kgat96/ubermini/hardware/cc2400dbk/CC2430-CC2591EM_2_0_Schematic.pdf

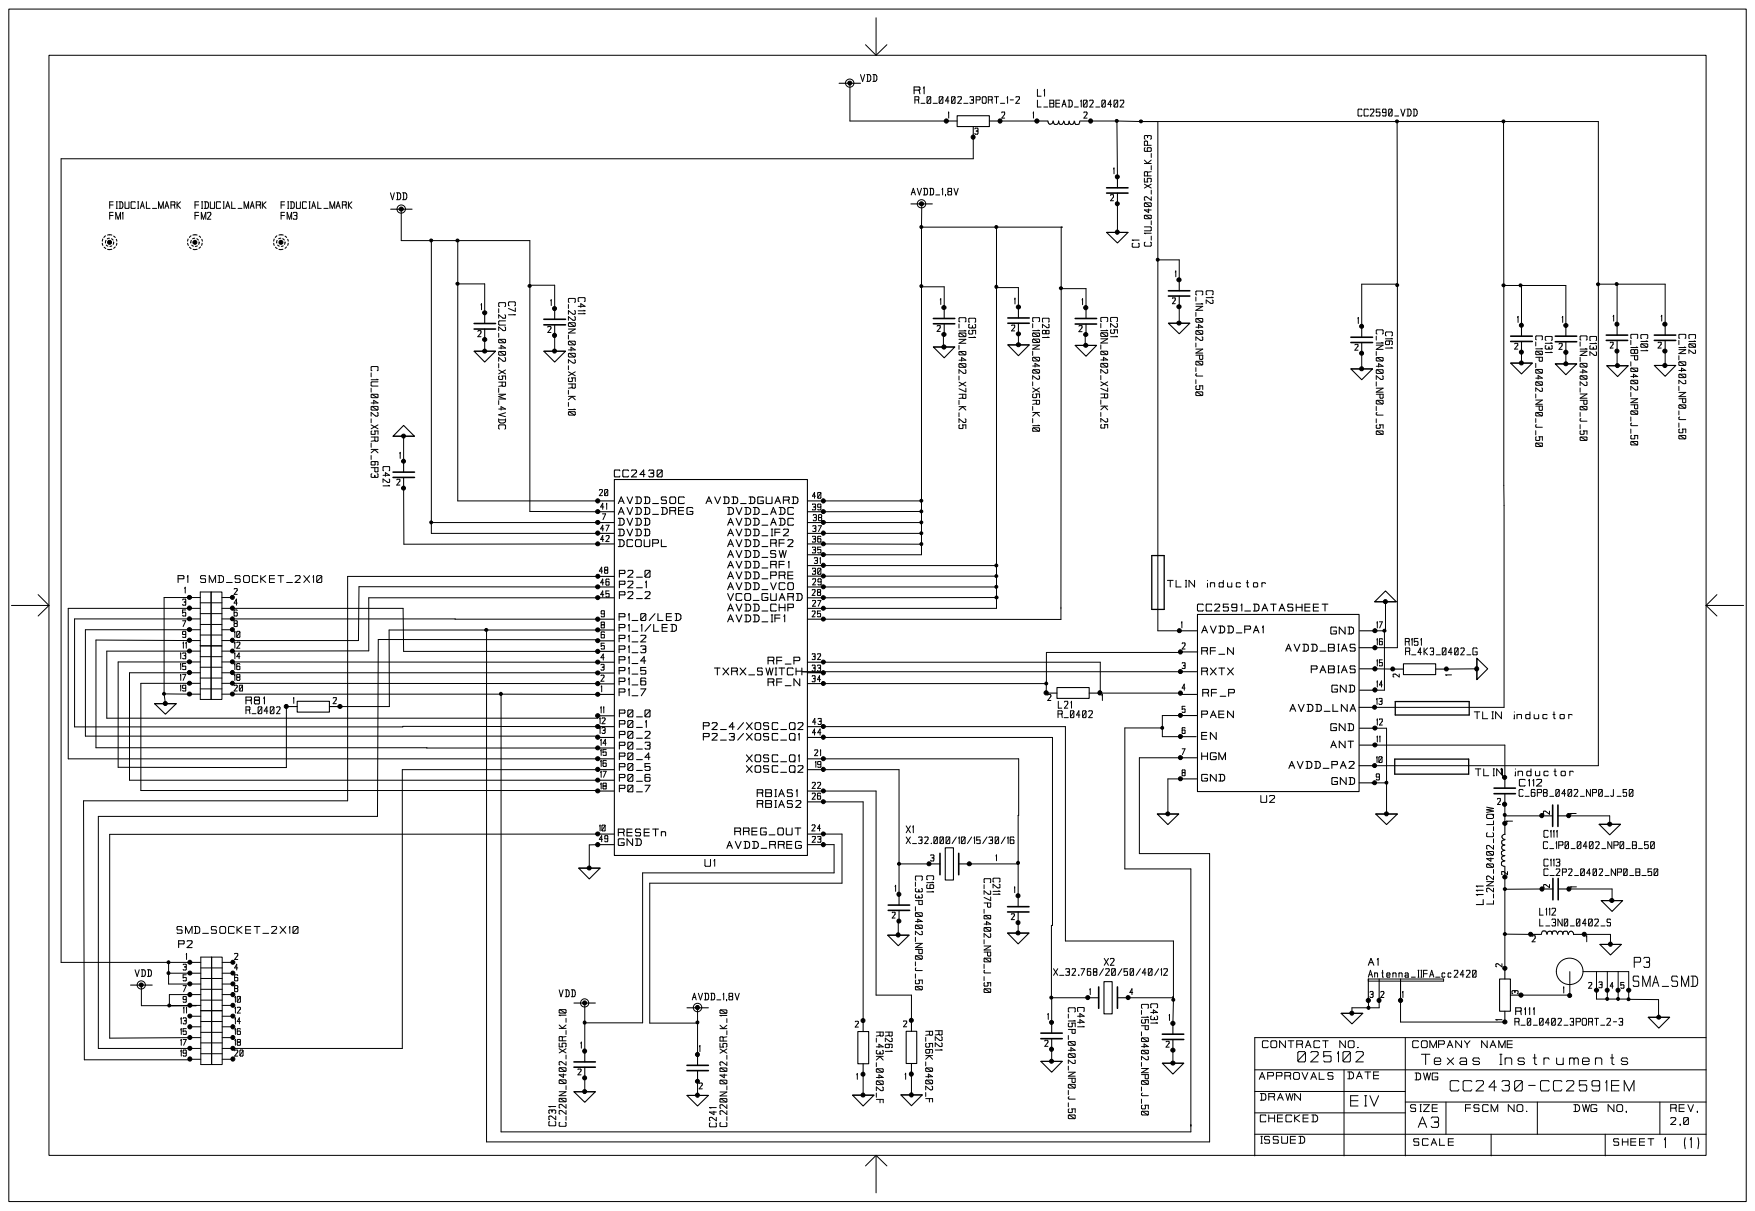
[picture p29: page 1]
