kgat96/ubermini/hardware/v1/ubertoothpV1.pdf

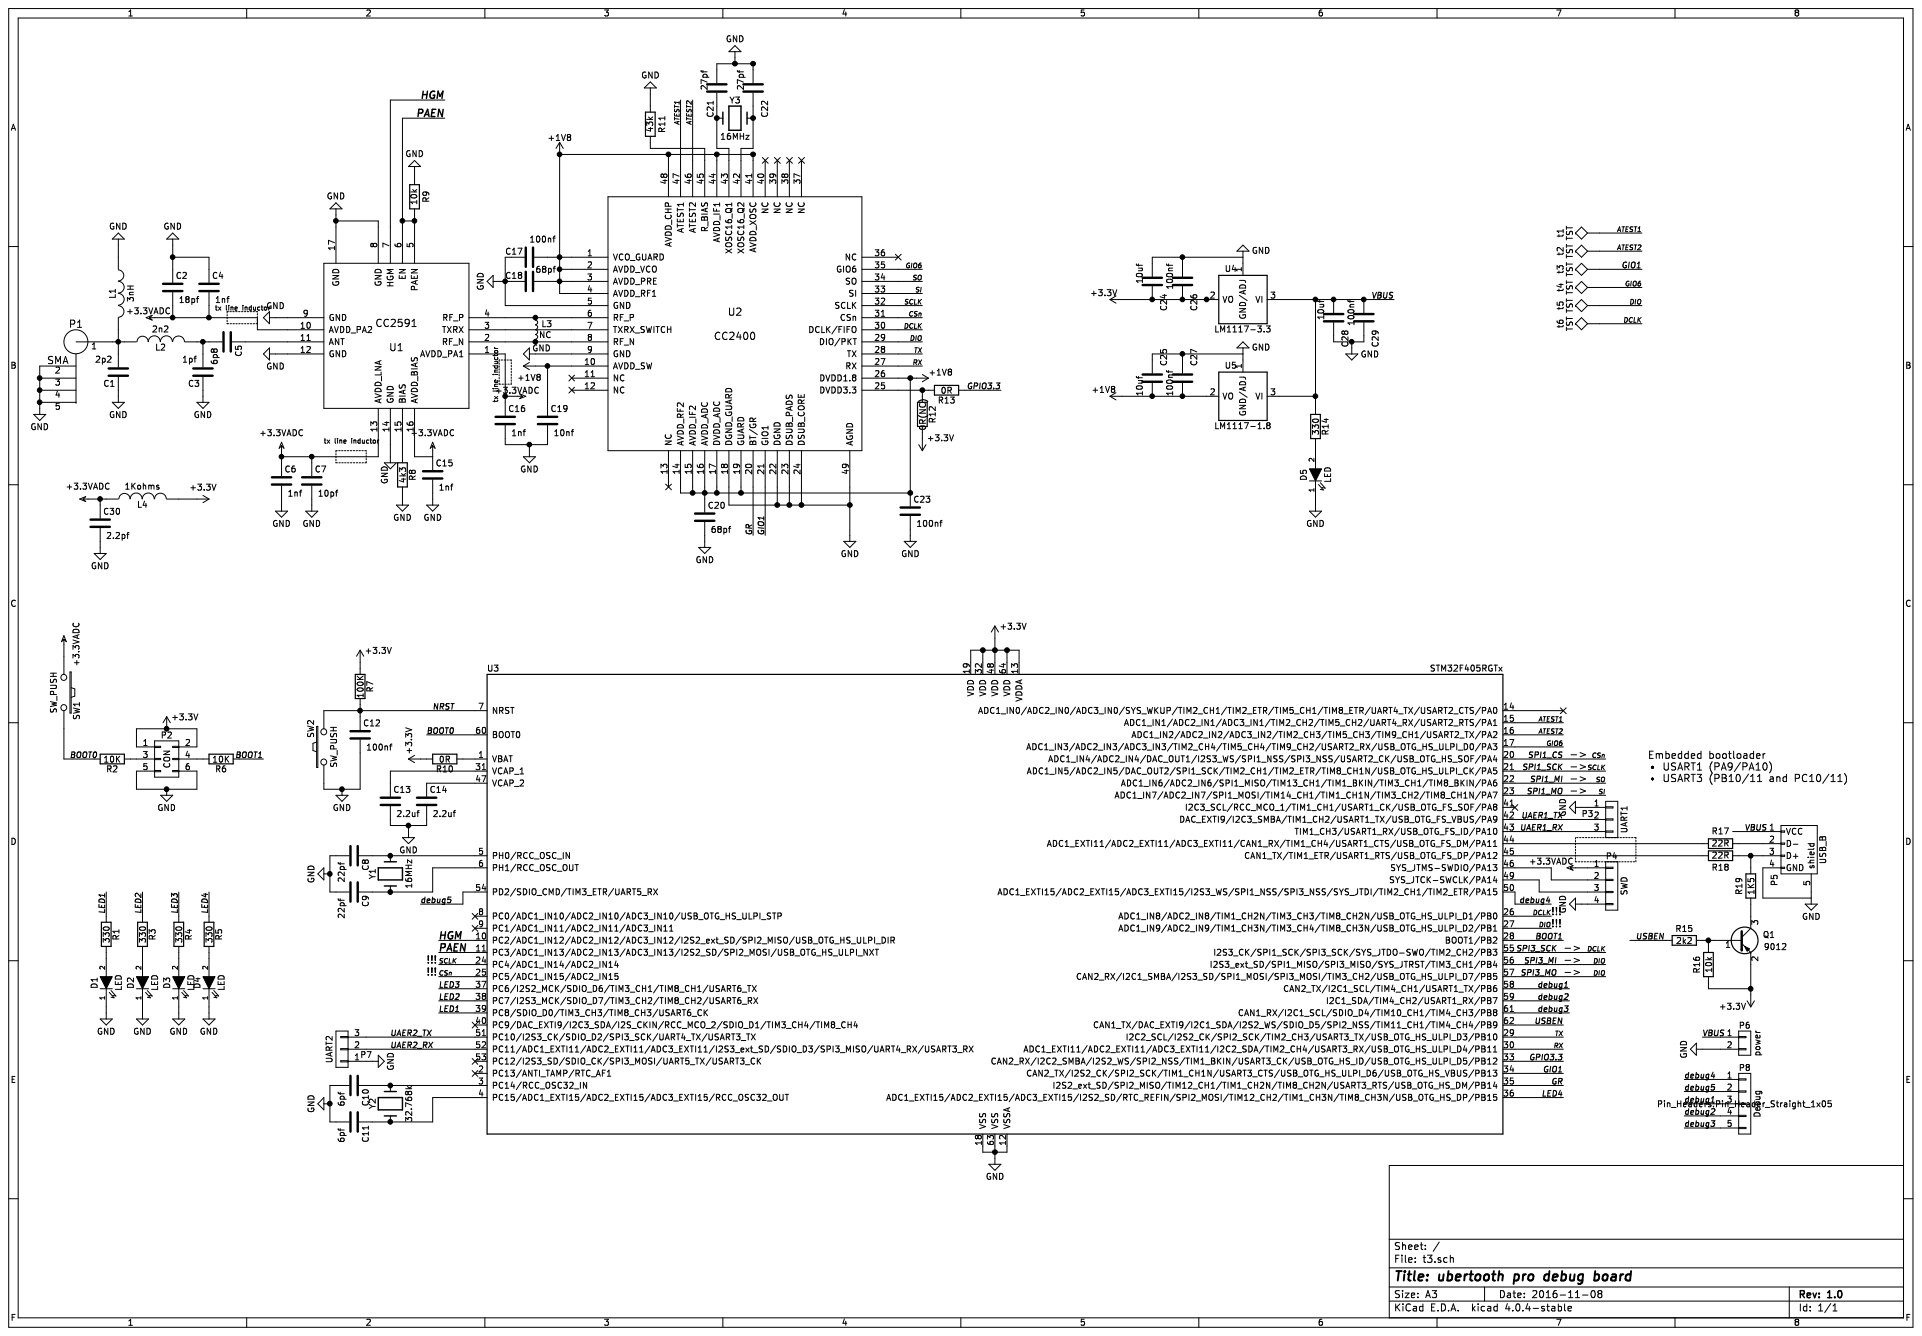
[picture p30: page 1]
