kgat96/ubermini/uber/hardware/artichoke/artichoke.sch

## KiCad design uber/hardware/artichoke/artichoke.sch (2016-11-08)

Schematic: artichoke.sch

Parts:
C1, C4, C22: 100nF
C2, C3, C6, C9, C15, C18, C20, C21: 27pF
C5, C17, C19: 220nF
C12, C16: 1pF; 0402
C13, C14: 10nF
C23, C24: 18pF
C25: 1µF; 0603
C26, C27, C28, C30, C31, C33, C34: 100nF; 0603
C29: 2.2µF; 0603
C32, C35: 18pF; 0603
D2: TXLED; 0603D
D3: RXLED; 0603D
D4: USRLED; 0603D
D5: RSTLED; 0603D
D6: USBLED; 0603D
J1: USB-DEVICE; USB-A-USAM-04
L1, L3: 2n7
L2: 9n5
P1: SMA-CONN; SMA-EDGE
P2: PROGRAM; 100MIL-HEADER-1X6-EDGE
P3: JTAG; 50MIL-HEADER-2X5-TH
P4: EXPAND; PIN_ARRAY_3X2
P6: 3V3D; testpad-50mil
P7: VBUS; testpad-50mil
P8: ATB
P11: TRCLK; testpad-50mil
P12: DT; testpad-50mil
P13: DR; testpad-50mil
Q1: BC856; SOT416
R1, R9, R10, R14: 10k; 0603
R2: 27k
R5, R6: 470; 0603
R7, R8, R15: 330; 0603
R11: 2k2; 0603
R12, R13: 33; 0603
R16: 1k5; 0603
U1: SI9183-A
U2: ADF7242
U4: LPC175X; LQFP80
U6: IP4220CZ6; SOT457
X1: NX3225SA; ABMM2
X2: ABM8G

Notes on the sheet:
test points
expansion connector
JTAG connector
programming connector
