kgat96/ubermini/uber/hardware/tc13badge/tc13badge.sch

## KiCad design uber/hardware/tc13badge/tc13badge.sch (2016-11-08)

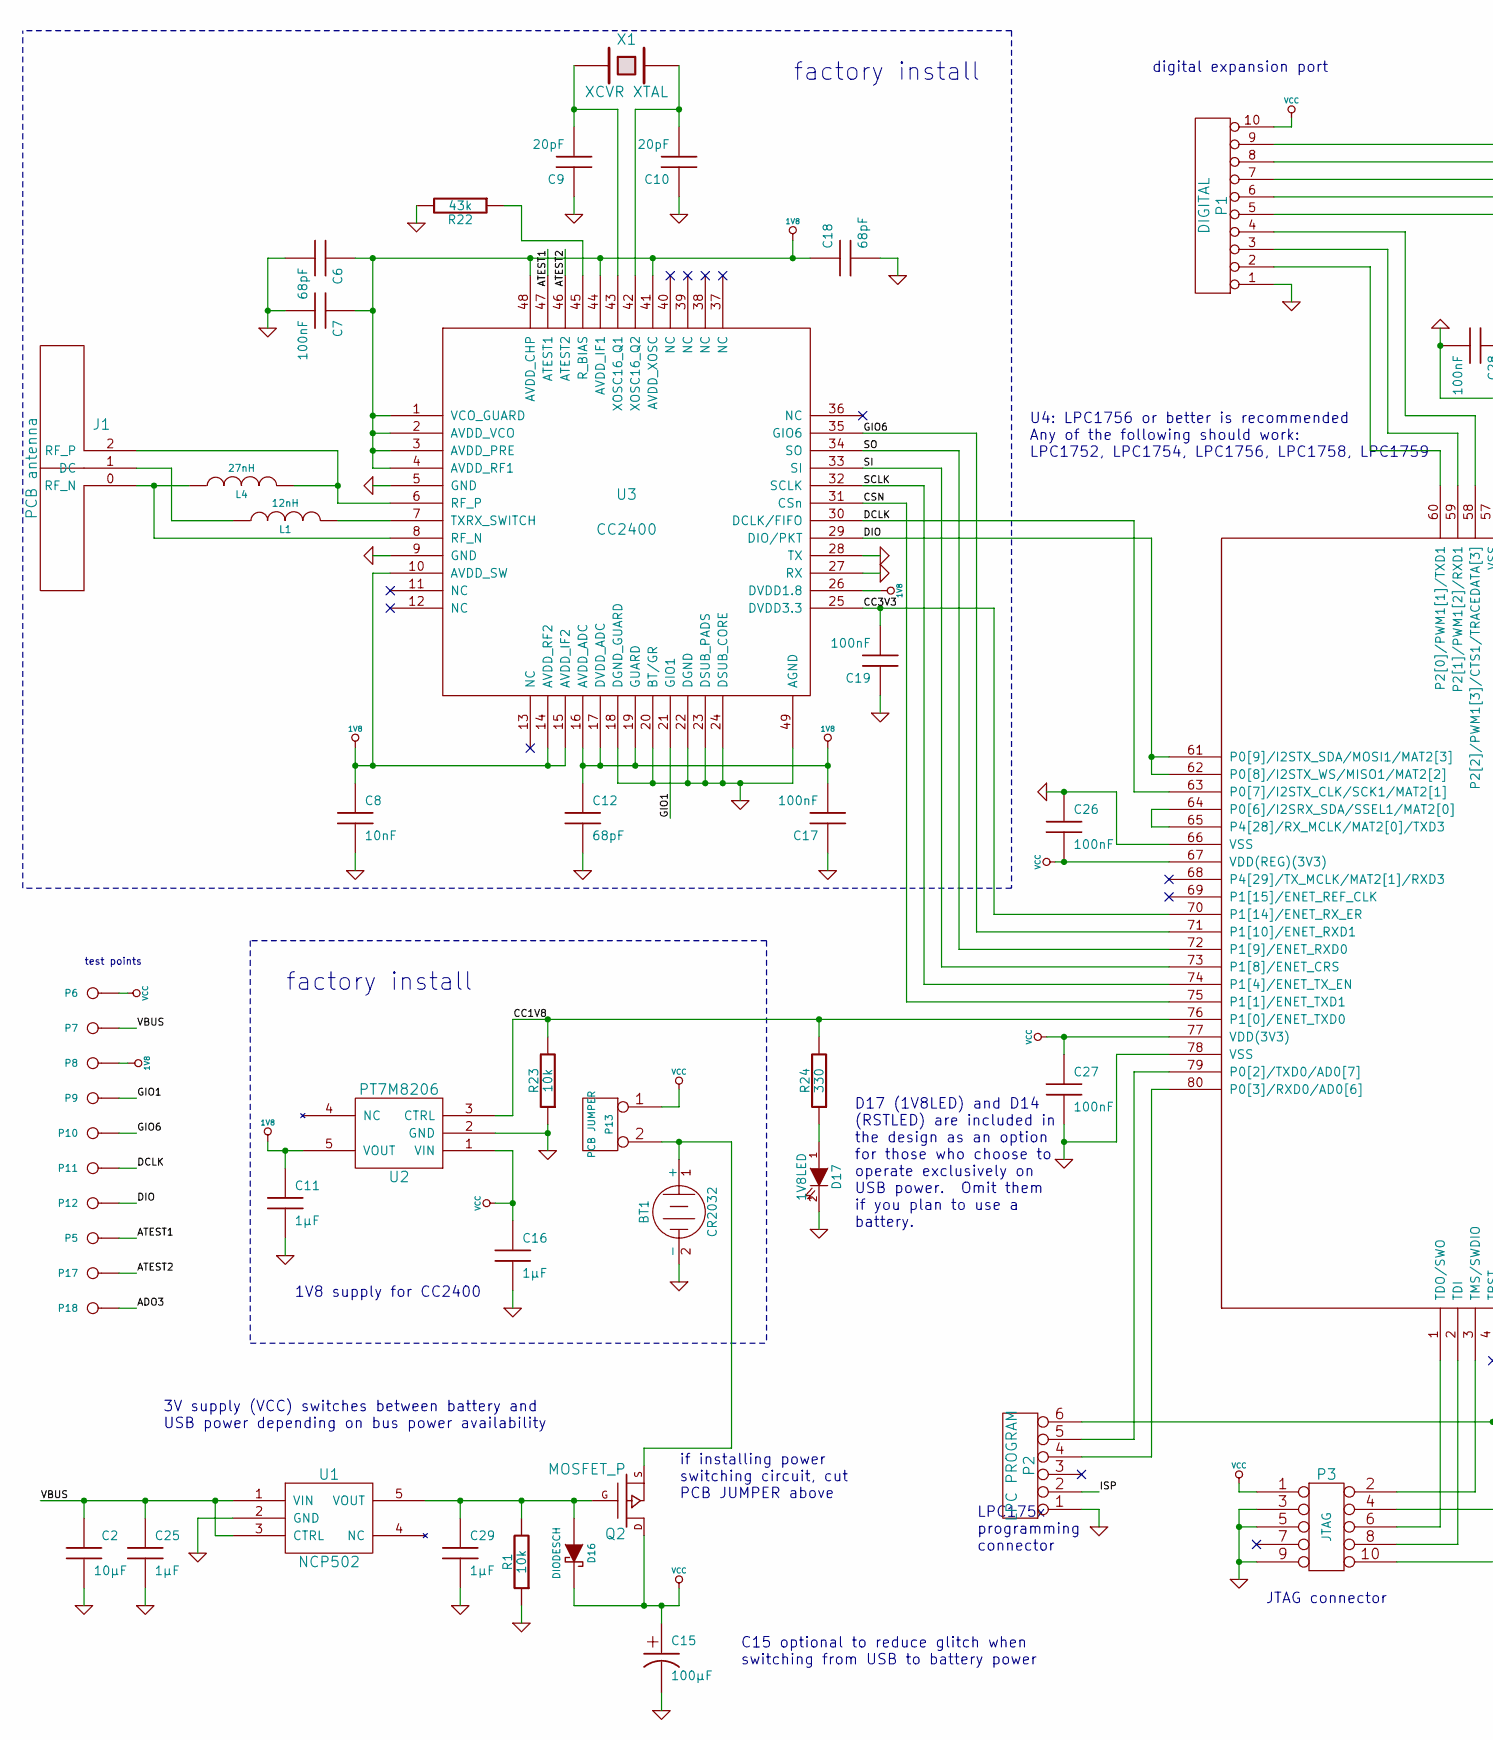
[picture p44: schematic tc13badge.sch, part in row 1, column 1]

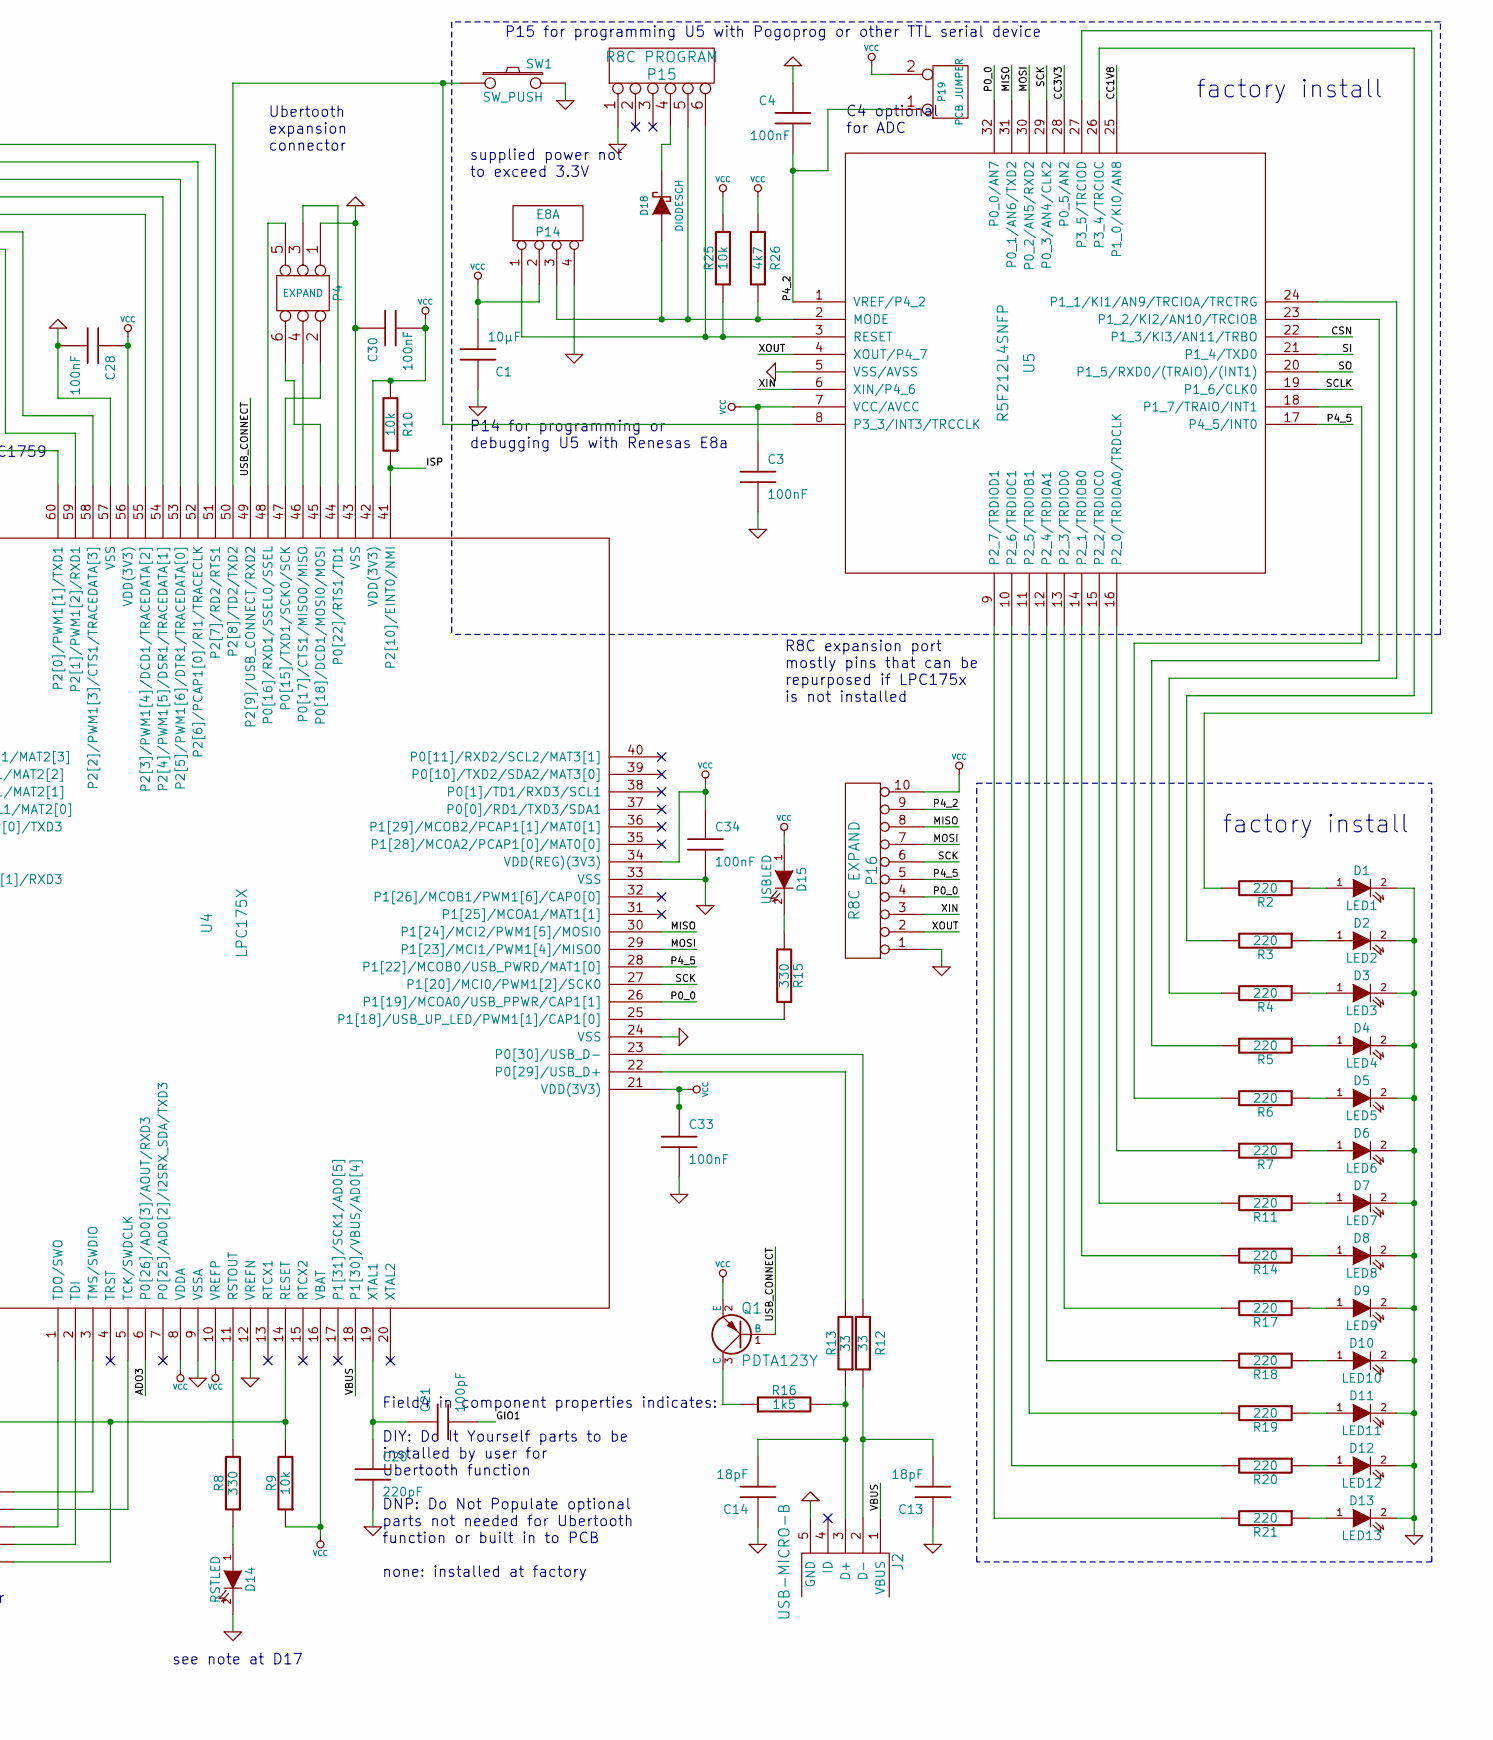
[picture p45: schematic tc13badge.sch, part in row 1, column 2]

Parts:
BT1: CR2032; GSG-BK-912
C1, C2: 10µF; GSG-1206
C3, C7, C17, C19: 100nF; 0402
C4, C26, C27, C28, C30, C33, C34: 100nF; 0603
C6, C12, C18: 68pF; 0402
C8: 10nF; 0402
C9, C10: 20pF; 0603
C11, C16, C25, C29: 1µF; 0603
C13, C14: 18pF; 0603
C15: 100µF; GSG-UUR1C101MCL1GS
C20: 220pF; 0603
C21: 100pF; 0603
D1: LED1; GSG-1206D
D2: LED2; GSG-1206D
D3: LED3; GSG-1206D
D4: LED4; GSG-1206D
D5: LED5; GSG-1206D
D6: LED6; GSG-1206D
D7: LED7; GSG-1206D
D8: LED8; GSG-1206D
D9: LED9; GSG-1206D
D10: LED10; GSG-1206D
D11: LED11; GSG-1206D
D12: LED12; GSG-1206D
D13: LED13; GSG-1206D
D14: RSTLED; 0603D
D15: USBLED; 0603D
D16, D18: DIODESCH; GSG-SOD-523F
D17: 1V8LED; 0603D
J1: PCB antenna; GSG-2.4GHz-FOLDED-DIPOLE
J2: USB-MICRO-B; GSG-USB-MICROB-FCI-10103594
L1: 12nH; 0402
L4: 27nH; 0402gap
P1: DIGITAL; PIN_ARRAY_5x2
P2: LPC PROGRAM; PIN_ARRAY-6X1
P3: JTAG; 50MIL-HEADER-2X5-TH
P4: EXPAND; PIN_ARRAY_3X2
P5: ATEST1; testpad-50mil
P6: VCC; testpad-50mil
P7: VBUS; testpad-50mil
P8: 1V8; testpad-50mil
P9: GIO1; testpad-50mil
P10: GIO6; testpad-50mil
P11: DCLK; testpad-50mil
P12: DIO; testpad-50mil
P13, P19: PCB JUMPER; 0603bridged
P14: E8A; PIN_ARRAY-4X1
P15: R8C PROGRAM; PIN_ARRAY-6X1
P16: R8C EXPAND; PIN_ARRAY_5x2
P17: ATEST2; testpad-50mil
P18: ADO3; testpad-50mil
Q1: PDTA123Y; SOT416
Q2: MOSFET_P; SOT23GDS
R1, R9, R10, R23, R25: 10k; 0603
R2, R3, R4, R5, R6, R7, R11, R14, R17, R18, R19, R20, R21: 220; 0603
R8, R15, R24: 330; 0603
R12, R13: 33; 0603
R16: 1k5; 0603
R22: 43k; 0402
R26: 4k7; 0603
SW1: SW_PUSH; GSG-SPST-FSM4JSMATR
U1: NCP502; GSG-SC70-5
U2: PT7M8206; SOT23-5
U3: CC2400; QFN48
U4: LPC175X; LQFP80
U5: R5F212L4SNFP; GSG-P-LQFP32-7x7-0.80
X1: XCVR XTAL; GSG-HC-49S

Connections:
1V8: C6.1, C7.1, C8.1, C11.1, C12.1, C17.2, C18.1, P8.1, U2.5 (VOUT), U3.1 (VCO_GUARD), U3.2 (AVDD_VCO), U3.3 (AVDD_PRE), U3.4 (AVDD_RF1), U3.10 (AVDD_SW), U3.14 (AVDD_RF2), U3.15 (AVDD_IF2), U3.16 (AVDD_ADC), U3.17 (DVDD_ADC), U3.19 (GUARD), U3.26 (DVDD1.8), U3.41 (AVDD_XOSC), U3.44 (AVDD_IF1), U3.48 (AVDD_CHP)
ADO3: P18.1, U4.6 (P0[26]/AD0[3]/AOUT/RXD3)
ATEST1: P5.1, U3.47 (ATEST1)
ATEST2: P17.1, U3.46 (ATEST2)
CC1V8: R23.2, R24.2, U2.3 (CTRL), U4.76 (P1[0]/ENET_TXD0), U5.25 (P1_0/KI0/AN8)
CC3V3: C19.2, U3.25 (DVDD3.3), U4.70 (P1[14]/ENET_RX_ER), U5.28 (P0_5/AN2)
CSN: U3.31 (CSn), U4.75 (P1[1]/ENET_TXD1), U5.22 (P1_3/KI3/AN11/TRBO)
DCLK: P11.1, U3.30 (DCLK/FIFO), U4.63 (P0[7]/I2STX_CLK/SCK1/MAT2[1])
DIO: P12.1, U3.29 (DIO/PKT), U4.61 (P0[9]/I2STX_SDA/MOSI1/MAT2[3]), U4.62 (P0[8]/I2STX_WS/MISO1/MAT2[2])
GIO1: C21.2, P9.1, U3.21 (GIO1)
GIO6: P10.1, U3.35 (GIO6), U4.71 (P1[10]/ENET_RXD1)
GND: BT1.2 (-), C1.1, C2.2, C3.2, C4.1, C6.2, C7.2, C8.2, C9.1, C10.1, C11.2, C12.2, C13.1, C14.1, C15.2, C16.2, C17.1, C18.2, C19.1, C20.2, C25.2, C26.1, C27.2, C28.2, C29.2, C30.1, C33.2, C34.2, D1.2 (K), D2.2 (K), D3.2 (K), D4.2 (K), D5.2 (K), D6.2 (K), D7.2 (K), D8.2 (K), D9.2 (K), D10.2 (K), D11.2 (K), D12.2 (K), D13.2 (K), D14.2 (K), D17.2 (K), J2.5 (GND), P1.1, P2.1, P3.3, P3.5, P3.9, P4.1, P14.4, P15.1, P16.1, R1.1, R22.2, R23.1, SW1.2, U1.2 (GND), U2.2 (GND), U3.5 (GND), U3.9 (GND), U3.18 (DGND_GUARD), U3.20 (BT/GR), U3.22 (DGND), U3.23 (DSUB_PADS), U3.24 (DSUB_CORE), U3.27 (RX), U3.28 (TX), U3.49 (AGND), U4.9 (VSSA), U4.12 (VREFN), U4.24 (VSS), U4.33 (VSS), U4.43 (VSS), U4.57 (VSS), U4.66 (VSS), U4.78 (VSS), U5.5 (VSS/AVSS)
ISP: P2.2, R10.1, U4.41 (P2[10]/EINT0/NMI)
MISO: P16.8, U4.30 (P1[24]/MCI2/PWM1[5]/MOSI0), U5.31 (P0_1/AN6/TXD2)
MOSI: P16.7, U4.29 (P1[23]/MCI1/PWM1[4]/MISO0), U5.30 (P0_2/AN5/RXD2)
unnamed: BT1.1 (+), P13.2 (PM), Q2.S
unnamed: C9.2, U3.43 (XOSC16_Q1), X1.1
unnamed: C10.2, U3.42 (XOSC16_Q2), X1.2
unnamed: C13.2, J2.2 (D-), R12.1
unnamed: C14.2, J2.3 (D+), R13.1, R16.2
unnamed: C20.1, C21.1, U4.19 (XTAL1)
unnamed: C29.1, D16.1 (A), Q2.G, R1.2, U1.5 (VOUT)
unnamed: D1.1 (A), R2.1
unnamed: D2.1 (A), R3.1
unnamed: D3.1 (A), R4.1
unnamed: D4.1 (A), R5.1
unnamed: D5.1 (A), R6.1
unnamed: D6.1 (A), R7.1
unnamed: D7.1 (A), R11.1
unnamed: D8.1 (A), R14.1
unnamed: D9.1 (A), R17.1
unnamed: D10.1 (A), R18.1
unnamed: D11.1 (A), R19.1
unnamed: D12.1 (A), R20.1
unnamed: D13.1 (A), R21.1
unnamed: D14.1 (A), R8.1
unnamed: D15.2 (K), R15.1
unnamed: D17.1 (A), R24.1
unnamed: D18.1 (A), P14.3, P15.5, R26.1, U5.2 (MODE)
unnamed: D18.2 (K), P15.4
unnamed: J1.0 (RF_N), L4.1, U3.8 (RF_N)
unnamed: J1.1 (DC), L1.1
unnamed: J1.2 (RF_P), L4.2, U3.6 (RF_P)
unnamed: L1.2, U3.7 (TXRX_SWITCH)
unnamed: P1.2, U4.60 (P2[0]/PWM1[1]/TXD1)
unnamed: P1.3, U4.59 (P2[1]/PWM1[2]/RXD1)
unnamed: P1.4, U4.58 (P2[2]/PWM1[3]/CTS1/TRACEDATA[3])
unnamed: P1.5, U4.55 (P2[3]/PWM1[4]/DCD1/TRACEDATA[2])
unnamed: P1.6, U4.54 (P2[4]/PWM1[5]/DSR1/TRACEDATA[1])
unnamed: P1.7, U4.53 (P2[5]/PWM1[6]/DTR1/TRACEDATA[0])
unnamed: P1.8, U4.52 (P2[6]/PCAP1[0]/RI1/TRACECLK)
unnamed: P1.9, U4.51 (P2[7]/RD2/RTS1)
unnamed: P2.4, U4.80 (P0[3]/RXD0/AD0[6])
unnamed: P2.5, U4.79 (P0[2]/TXD0/AD0[7])
unnamed: P2.6, P3.10, R9.2, U4.14 (RESET)
unnamed: P3.2, U4.3 (TMS/SWDIO)
unnamed: P3.4, U4.5 (TCK/SWDCLK)
unnamed: P3.6, U4.1 (TDO/SWO)
unnamed: P3.8, U4.2 (TDI)
unnamed: P4.2, U4.47 (P0[15]/TXD1/SCK0/SCK)
unnamed: P4.3, U4.44 (P0[22]/RTS1/TD1)
unnamed: P4.4, U4.46 (P0[17]/CTS1/MISO0/MISO)
unnamed: P4.5, U4.48 (P0[16]/RXD1/SSEL0/SSEL)
unnamed: P4.6, U4.45 (P0[18]/DCD1/MOSI0/MOSI)
unnamed: P14.1, P15.6, R25.1, U5.3 (RESET)
unnamed: Q1.3 (C), R16.1
unnamed: R2.2, U5.27 (P3_5/TRCIOD)
unnamed: R3.2, U5.26 (P3_4/TRCIOC)
unnamed: R4.2, U5.24 (P1_1/KI1/AN9/TRCIOA/TRCTRG)
unnamed: R5.2, U5.23 (P1_2/KI2/AN10/TRCIOB)
unnamed: R6.2, U5.18 (P1_7/TRAIO/INT1)
unnamed: R7.2, U5.16 (P2_0/TRDIOA0/TRDCLK)
unnamed: R8.2, U4.11 (RSTOUT)
unnamed: R11.2, U5.15 (P2_2/TRDIOC0)
unnamed: R12.2, U4.23 (P0[30]/USB_D-)
unnamed: R13.2, U4.22 (P0[29]/USB_D+)
unnamed: R14.2, U5.14 (P2_1/TRDIOB0)
unnamed: R15.2, U4.25 (P1[18]/USB_UP_LED/PWM1[1]/CAP1[0])
unnamed: R17.2, U5.13 (P2_3/TRDIOD0)
unnamed: R18.2, U5.12 (P2_4/TRDIOA1)
unnamed: R19.2, U5.11 (P2_5/TRDIOB1)
unnamed: R20.2, U5.10 (P2_6/TRDIOC1)
unnamed: R21.2, U5.9 (P2_7/TRDIOD1)
unnamed: R22.1, U3.45 (R_BIAS)
unnamed: SW1.1, U4.50 (P2[8]/TD2/TXD2), U5.8 (P3_3/INT3/TRCCLK)
unnamed: U4.64 (P0[6]/I2SRX_SDA/SSEL1/MAT2[0]), U4.65 (P4[28]/RX_MCLK/MAT2[0]/TXD3)
P0_0: P16.4, U4.26 (P1[19]/MCOA0/USB_PPWR/CAP1[1]), U5.32 (P0_0/AN7)
P4_2: C4.2, P16.9, P19.1, U5.1 (VREF/P4_2)
P4_5: P16.5, U4.28 (P1[22]/MCOB0/USB_PWRD/MAT1[0]), U5.17 (P4_5/INT0)
SCK: P16.6, U4.27 (P1[20]/MCI0/PWM1[2]/SCK0), U5.29 (P0_3/AN4/CLK2)
SCLK: U3.32 (SCLK), U4.74 (P1[4]/ENET_TX_EN), U5.19 (P1_6/CLK0)
SI: U3.33 (SI), U4.73 (P1[8]/ENET_CRS), U5.21 (P1_4/TXD0)
SO: U3.34 (SO), U4.72 (P1[9]/ENET_RXD0), U5.20 (P1_5/RXD0/(TRAIO)/(INT1))
USB_CONNECT: Q1.1 (B), U4.49 (P2[9]/USB_CONNECT/RXD2)
VBUS: C2.1, C25.1, J2.1 (VBUS), P7.1, U1.1 (VIN), U1.3 (CTRL), U4.18 (P1[30]/VBUS/AD0[4])
VCC: C1.2, C3.1, C15.1, C16.1, C26.2, C27.1, C28.1, C30.2, C33.1, C34.1, D15.1 (A), D16.2 (K), P1.10, P3.1, P6.1, P13.1, P14.2, P16.10, P19.2 (PM), Q1.2 (E), Q2.D, R9.1, R10.2, R25.2, R26.2, U2.1 (VIN), U4.8 (VDDA), U4.10 (VREFP), U4.16 (VBAT), U4.21 (VDD(3V3)), U4.34 (VDD(REG)(3V3)), U4.42 (VDD(3V3)), U4.56 (VDD(3V3)), U4.67 (VDD(REG)(3V3)), U4.77 (VDD(3V3)), U5.7 (VCC/AVCC)
XIN: P16.3, U5.6 (XIN/P4_6)
XOUT: P16.2, U5.4 (XOUT/P4_7)

Notes on the sheet:
see note at D17
D17 (1V8LED) and D14 (RSTLED) are included in the design as an option for those who choose to operate exclusively on USB power. Omit them if you plan to use a battery.
U4: LPC1756 or better is recommended Any of the following should work: LPC1752, LPC1754, LPC1756, LPC1758, LPC1759
P15 for programming U5 with Pogoprog or other TTL serial device
P14 for programming or debugging U5 with Renesas E8a
supplied power not to exceed 3.3V
C4 optional for ADC
Field4 in component properties indicates: DIY: Do It Yourself parts to be installed by user for Ubertooth function DNP: Do Not Populate optional parts not needed for Ubertooth function or built in to PCB none: installed at factory
if installing power switching circuit, cut PCB JUMPER above
factory install
R8C expansion port mostly pins that can be repurposed if LPC175x is not installed
C15 optional to reduce glitch when switching from USB to battery power
1V8 supply for CC2400
3V supply (VCC) switches between battery and USB power depending on bus power availability
digital expansion port
test points
Ubertooth expansion connector
JTAG connector
LPC175x programming connector
