kgat96/ubermini/firmware/v2pro4_connect/ble.c

/*
 * This file is part of the ubermini project.
 *
 * Copyright (C) 2017 Kage Shen <kgat96@gmail.com>
 *
 * This program is free software; you can redistribute it and/or modify
 * it under the terms of the GNU General Public License version 2 as
 * published by the Free Software Foundation.
 */

#include <string.h>

#include <libopencm3/stm32/timer.h>

#include "config.h"
#include "cc.h"
#include "uart.h"
#include "ble.h"

void delay_us(u32 us);
void delay_ms(u32 us);

//0x40, 0xb2, 0xbc, 0xc3, 0x1f, 0x37, 0x4a, 0x5f, 0x85,
//0xf6, 0x9c, 0x9a, 0xc1, 0xd6, 0xc5, 0x44, 0x20, 0x59,
//0xde, 0xe1, 0x8f, 0x1b, 0xa5, 0xaf, 0x42, 0x7b, 0x4e,
//0xcd, 0x60, 0xeb, 0x62, 0x22, 0x90, 0x2c, 0xef, 0xf0,
//0xc7, 0x8d, 0xd2, 0x57, 0xa1, 0x3d, 0xa7, 0x66, 0xb0,
//0x75, 0x31, 0x11, 0x48, 0x96, 0x77, 0xf8, 0xe3, 0x46,
//0xe9, 0xab, 0xd0, 0x9e, 0x53, 0x33, 0xd8, 0xba, 0x98,
//0x08, 0x24, 0xcb, 0x3b, 0xfc, 0x71, 0xa3, 0xf4, 0x55,
//0x68, 0xcf, 0xa9, 0x19, 0x6c, 0x5d, 0x4c, 0x04, 0x92,
//0xe5, 0x1d, 0xfe, 0xb8, 0x51, 0xfa, 0x2a, 0xb4, 0xe7,
//0xd4, 0x0c, 0xb6, 0x2e, 0x26, 0x02, 0xc9, 0xf2, 0x0e,
//0x7f, 0xdc, 0x28, 0x7d, 0x15, 0xda, 0x73, 0x6a, 0x06,
//0x5b, 0x17, 0x13, 0x81, 0x64, 0x79, 0x87, 0x3f, 0x6e,
//0x94, 0xbe, 0x0a, 0xed, 0x39, 0x35, 0x83, 0xad, 0x8b, 0x89,

//static const u32 whitening[40] = {
//        0x40, 0x89, 0xd2, 0x1b, 0x64, 0xad, 0xf6, 0x3f, 0x08, 0xc1,
//        0x9a, 0x53, 0x2c, 0xe5, 0xbe, 0x77, 0xd0, 0x19, 0x42, 0x8b,
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
    0x8c6e00, 0x8ddac0, 0x8f0780, 0x8eb340, 0x8abd00, 0x8b09c0, 0x89d480, 0x886040,
    0x9a8400, 0x9b30c0, 0x99ed80, 0x985940, 0x9c5700, 0x9de3c0, 0x9f3e80, 0x9e8a40,
    0x972200, 0x9696c0, 0x944b80, 0x95ff40, 0x91f100, 0x9045c0, 0x929880, 0x932c40
};

/*
 * Calculate a BTLE CRC one byte at a time. Thanks to Dominic Spill and
 * Michael Ossmann for writing and optimizing this.
 *
 * Arguments: CRCInit, pointer to start of packet, length of packet in
 * bytes
 * */
static u32 btle_crcgen_lut(u32 crc_init, u8 *data, int len)
{
    u32 state;
    int i;
    u8 key;

    state = crc_init & 0xffffff;
    for (i = 0; i < len; ++i) {
        key = data[i] ^ (state & 0xff);
        state = (state >> 8) ^ btle_crc_lut[key];
    }
    return state;
}

typedef enum {
    LINK_INACTIVE,
    LINK_SEND_ADV,
    LINK_SCAN_RSP,
    LINK_LISTENING,
    LINK_CONN_PENDING,
    LINK_CONNECTED,
} link_state_t;

typedef enum {
    LL_CONNECTION_UPDATE_REQ,
    LL_CHANNEL_MAP_REQ,
    LL_TERMINATE_IND,
    LL_ENC_REQ,
    LL_ENC_RSP,
    LL_START_ENC_REQ,
    LL_START_ENC_RSP,
    LL_UNKNOWN_RSP,
    LL_FEATURE_REQ,
    LL_FEATURE_RSP,
    LL_PAUSE_ENC_REQ,
    LL_PAUSE_ENC_RSP,
    LL_VERSION_IND,
    LL_REJECT_IND,
} ll_control_opcodes_t;

typedef struct _le_state_t {
    u32 access_address;         // Access Address to filter by
    u16 synch;                  // Access address in CC2400 syncword format
    u16 syncl;                  // lower 16 bits thereof
    u32 crc_init;               // CrcInit: used to calculate CRC
    u32 crc_init_reversed;      // bits-reversed version of the previous
    int crc_verify;             // true to reject packets with bad CRC

    link_state_t link_state;    // current link layer state

    u8 channel_idx;             // current channel index
    u8 channel_increment;       // amount to hop
    u8 sn;
    u8 nesn;

    u32 conn_epoch;             // reference time for the start of the connection
    u16 volatile interval_timer;// number of intervals remaining before next hop
    u16 conn_interval;          // connection-specific hop interval
    u16 volatile conn_count;    // number of intervals since the start of the connection

    u32 win_size;                // window size (max packets per connection)
    u32 win_offset;              // offset of first window from start of connection

    int update_pending;         // whether a connection update is pending
    u16 update_instant;         // the connection count when the update takes effect
    u16 interval_update;        // the new hop_internal
    u8 win_size_update;         // the new window size
    u16 win_offset_update;      // the new window offset

    u8 target[6];               // target MAC for connection following (byte order reversed)
    int target_set;             // whether a target has been set (default: false)
    u32 last_packet;            // when was the last packet received

    u32 tx_interval;
    u32 rx_interval;
} le_state_t;

le_state_t le;

static void le_set_access_address(u32 aa)
{
    u32 aa_rev;

    le.access_address = aa;
    aa_rev = rbit(aa);
    le.syncl = aa_rev & 0xffff;
    le.synch = aa_rev >> 16;
}

/* reset le state, called by bt_generic_le and bt_follow_le() */
static void ble_reset(void)
{
    le_set_access_address(0x8e89bed6);     // 0x8e89bed6 advertising channel access address
    le.crc_init  = 0x555555;               // advertising channel CRCInit
    le.crc_init_reversed = 0xAAAAAA;
    le.crc_verify = 0;
    le.last_packet = 0;

    le.link_state = LINK_SEND_ADV;

    le.channel_idx = 0;
    le.channel_increment = 0;

    le.conn_epoch = 0;
    le.interval_timer = 0;
    le.conn_interval = 0;
    le.conn_interval = 0;
    le.conn_count = 0;

    le.win_size = 0;
    le.win_offset = 0;

    le.update_pending = 0;
    le.update_instant = 0;
    le.interval_update = 0;
    le.win_size_update = 0;
    le.win_offset_update = 0;
}

static u16 btle_channel_index_to_phys(u8 idx) {
    u16 phys;
    if (idx < 11)
        phys = 2404 + 2 * idx;
    else if (idx < 37)
        phys = 2428 + 2 * (idx - 11);
    else if (idx == 37)
        phys = 2402;
    else if (idx == 38)
        phys = 2426;
    else
        phys = 2480;
    return phys;
}

static u8 btle_channel_index(u8 channel)
{
    u8 idx;
    channel /= 2;
    if (channel == 0)
        idx = 37;
    else if (channel < 12)
        idx = channel - 1;
    else if (channel == 12)
        idx = 38;
    else if (channel < 39)
        idx = channel - 2;
    else
        idx = 39;
    return idx;
}

static u16 btle_next_hop(le_state_t *lee)
{
    u16 phys = btle_channel_index_to_phys(lee->channel_idx);
    lee->channel_idx = (lee->channel_idx + lee->channel_increment) % 37;
    return phys;
}

static int btle_crc_verify(u8 *p, u32 len)
{
    u32 calc_crc = btle_crcgen_lut(le.crc_init_reversed, p + 4, len);
    u32 wire_crc = (p[4+len+2] << 16)
                 | (p[4+len+1] << 8)
                 | (p[4+len+0] << 0);

    return (calc_crc == wire_crc);
}

volatile u32 ble_packet_len = 0;
volatile u8 ble_rxpacket[128];
volatile u32 clk3125n = 0;

#define ADV_IND             0
#define ADV_DIRECT_IND      1
#define ADV_NONCONN_IND     2
#define SCAN_REQ            3
#define SCAN_RSP            4
#define CONNECT_REQ         5
#define ADV_SCAN_IND        6

static u8 adv_packet[] = {
    // LL header
    0, 0xff,
    // advertising address
    0x66, 0x55, 0x0, 0x56, 0x34, 0x12,
    // advertising data
    0x02, 0x01, 0x06,

    0x04, 0x08, 'K','K','S',
    // CRC (calc)
    0xff, 0xff, 0xff,
};

#define BT_ADDR     (&adv_packet[2])

u32 tim2_jiffies(u32 n);
int tim2_before(u32 t);
int tim2_after(u32 t);

static void adv_packet_send(u32 channel, u8 type)
{
    u8 advbuf[64];
    u32 aa = 0x8e89bed6;
    u32 adv_len = sizeof(adv_packet);

    adv_packet[0] = type;
    adv_packet[1] = adv_len - 5;
    u32 calc_crc = btle_crcgen_lut(0xAAAAAA, adv_packet, adv_len - 3);
    adv_packet[adv_len-3] = (calc_crc >>  0) & 0xff;
    adv_packet[adv_len-2] = (calc_crc >>  8) & 0xff;
    adv_packet[adv_len-1] = (calc_crc >> 16) & 0xff;

    u32 *ptx = (u32 *)advbuf;
    u32 *padv = (u32 *)adv_packet;

    ptx[0] = rev(rbit(aa));

    //u32 v = rev(rxp[i]);
    //packet[i+1] = rbit(v) ^ whit[i];
    const u32 *whit = whitening_word[btle_channel_index(channel-2402)];
    for (u32 i = 0; i < (adv_len+3)/4; i++) {
        u32 v = padv[i] ^ whit[i];
        ptx[i+1] = rev(rbit(v));
    }

    adv_len += 4;

#if 0
    // 6b 7d 91 71 6b 33 42 a4 ba bb c7 71 9d 20 50 f6 5f fd
    printf("whiten:");
    for (u32 i = 0; i < adv_len; i++) {
        //txbuf[i] = 0xff;
        printf("%x ", advbuf[i]);
    }
#endif

    while (tim2_before(le.tx_interval));

    rf_transfer(adv_len, advbuf);
}

static void ll_send_empty(void)
{
    //rf_txmode(rbit(le.access_address), advchannel);
    //adv_packet_send(advchannel, ADV_IND);


}

static void ll_control_packet(u8 *p, u32 len)
{
    ll_control_opcodes_t op;

    //u8 llid = p[4] & 3;
    u8 NESN = p[4] & BIT(2);
    u8 SN = p[4] & BIT(3);

    if (le.nesn != SN) {    // master 重发包 ?
        printf("master resend packet %d !\n", le.nesn);
        return;
    }

    le.nesn = !le.nesn;

    switch (op) {
    case LL_VERSION_IND:
        break;


    default:
        break;
    }
}

const u16 advchannel = 2426; // 2.426G

const u32 bletunit = (1.25*1000);

void ble_process(void)
{
    switch (le.link_state) {
    case LINK_SEND_ADV: {
        printf("tx adv packet\n");

        rf_txmode(rbit(le.access_address), advchannel);
        adv_packet_send(advchannel, ADV_IND);
        le.tx_interval = tim2_jiffies(500000);  // next tx time

        rf_rxmode(rbit(le.access_address), advchannel);
        spi_set_nss_low(SPI3);
        cx_strobe(SRX);

        u32 to = tim2_jiffies(500);             // receive packet 500us
        while (tim2_before(to)){
            if (ble_packet_len > 16) {          // > 16bytes
                u32 packet[48/4+1];
                u8 *p = (u8 *)packet;
                u32 *rxp = (u32 *)ble_rxpacket;
                packet[0] = le.access_address;
                le.tx_interval = tim2_jiffies(150);  // update next tx time

                const u32 *whit = whitening_word[btle_channel_index(advchannel-2402)];
                for (int i = 0; i < 4; i++) {       // > 16bytes
                    u32 v = rev(rxp[i]);
                    packet[i+1] = rbit(v) ^ whit[i];
                }

                if (!memcmp(p+12, BT_ADDR, 6)) {
                    memcpy(le.target, p+12, 6);
                    switch(p[4] & 0xf) {
                    case SCAN_REQ:
                        le.link_state = LINK_SCAN_RSP;
                        break;
                    case CONNECT_REQ:
                        while(ble_packet_len < 40);

                        for (int i = 4; i < (40/4); i++) {   // > 40bytes
                              u32 v = rev(rxp[i]);
                              packet[i+1] = rbit(v) ^ whit[i];
                        }

                        u32 pdu_len = (p[5] & 0x3f) + 2;    // PDU length
                        if (!btle_crc_verify(p, pdu_len)) {
                            printf("CONNECT_REQ CRC error\n");
                            break;
                        }

                        le.link_state = LINK_CONN_PENDING;

                        u32 access_address = 0;
                        #define ACCESS_ADDR_DFF     (4+2+6+6)
                        for (u32 i = 0; i < 4; ++i)
                            access_address |= p[ACCESS_ADDR_DFF+i] << (i*8);

                        le_set_access_address(access_address);

                        #define CRC_INIT            (4+2+6+6+4)
                        le.crc_init = (p[CRC_INIT+2] << 16)
                                    | (p[CRC_INIT+1] << 8)
                                    |  p[CRC_INIT+0];
                        le.crc_init &= 0xffffff;
                        le.crc_init_reversed = rbit(le.crc_init) >> 8;

                        #define WIN_SIZE            (4+2+6+6+4+3)
                        le.win_size = p[WIN_SIZE];

                        #define WIN_OFFSET          (4+2+6+6+4+3+1)
                        le.win_offset = p[WIN_OFFSET];

                        #define CONN_INTERVAL       (4+2+6+6+4+3+1+2)
                        le.conn_interval = (p[CONN_INTERVAL+1] << 8)
                                             | p[CONN_INTERVAL+0];

                        #define CHANNEL_INC         (4+2+6+6+4+3+1+2+2+2+2+5)
                        le.channel_increment = p[CHANNEL_INC] & 0x1f;
                        le.channel_idx = le.channel_increment;

                        printf("  -> CONNECT_ReQ\n");
                        printf("%x %x\n", le.access_address, le.synch);
                        printf("%x %x\n", le.crc_init, le.crc_init_reversed);
                        printf("%x %x\n", le.win_size, le.win_offset);
                        printf("%x %x\n", le.conn_interval, le.channel_increment);

                        le.conn_interval *= bletunit;
                        le.win_size *= bletunit;
                        le.win_offset = (le.win_offset + 1) * bletunit;

                        le.rx_interval = tim2_jiffies(le.win_offset);     // us
                        break;
                    }
                }

#if 0
                for (u32 i= 0; i < 20; i++) {
                    printf("%x ", p[i]);
                }
                kputc('\n');
#endif
                break;  // break while (tim2_before(to))
            }
        }

        spi_set_nss_high(SPI3);
        cc_clean_fifo();
        ble_packet_len = 0;
        cx_strobe(SRFOFF);

        //if (le.link_state == LINK_SEND_ADV)
        //    delay_ms(500);

        } break;
    case LINK_SCAN_RSP: {
        rf_txmode(rbit(le.access_address), advchannel);
        adv_packet_send(advchannel, SCAN_RSP);
        le.link_state = LINK_SEND_ADV;
        //delay_ms(500);
        printf("  -> SCAN_RSP\n");
        le.tx_interval = tim2_jiffies(500000);    // next tx time

        } break;
    case LINK_CONN_PENDING: {
        u16 channel = btle_next_hop(&le);
        rf_rxmode(rbit(le.access_address), channel);
        spi_set_nss_low(SPI3);

        //printf("  -> CONNECT_REQ\n");
        while(tim2_before(le.rx_interval));
        le.rx_interval = tim2_jiffies(le.conn_interval);

        cx_strobe(SRX);
        u32 to = tim2_jiffies(le.win_size);     // receive packet le.win_size
        while (tim2_before(to)){
            if (ble_packet_len > 4) {           // > 4bytes (PDU header)
                u32 packet[48/4+1];
                u8 *p = (u8 *)packet;
                u32 *rxp = (u32 *)ble_rxpacket;
                packet[0] = le.access_address;
                le.tx_interval = tim2_jiffies(150);         // update next tx time

                const u32 *whit = whitening_word[btle_channel_index(channel-2402)];
                for (int i = 0; i < 1; i++) {               // > 4bytes
                    u32 v = rev(rxp[i]);
                    packet[i+1] = rbit(v) ^ whit[i];
                }

                u32 pdu_len = (p[5] & 0x1f) + 2;             // PDU length
                while(ble_packet_len < (pdu_len + 2 + 3));  // whit all data

                if (!btle_crc_verify(p, pdu_len)) {
                    printf("LINK_CONN_PENDING CRC error\n");
                    break;
                }

                u8 llid = p[4] & 3;
                switch(llid) {
                case 3:                             //LL control PDU
                    ll_control_packet(p, pdu_len);
                    break;
                case 1:
                case 2:                             //L2CAP

                    break;
                }

                for (u32 i= 0; i < 12; i++) {
                    printf("%x ", p[i]);
                }
                kputc('\n');

                break;
            }
        }

        spi_set_nss_high(SPI3);
        cc_clean_fifo();
        ble_packet_len = 0;
        cx_strobe(SRFOFF);

        } break;
    default:
        break;
    }


//    while(1) {
//        delay_ms(300);
//        rf_transfer(adv_len, txbuf);
//        printf("send ADVx\n");
//    }
}

void ble_init(void)
{
    //volatile u16 channel = 2426;

    ble_packet_len = 0;
    ble_reset();
    rf_init(MOD_BT_LOW_ENERGY);

#if 0           // test rx
    kputs("bleR\n");
    rf_rxmode(rbit(le.access_address), channel);
    cx_strobe(SRX);
#else
    //kputs("bleT\n");
    //rf_txmode(rbit(le.access_address), channel);
#endif
}
